Roukie686868/Presence-Sensor/Documents/Pictures/IMG_2770.jpg

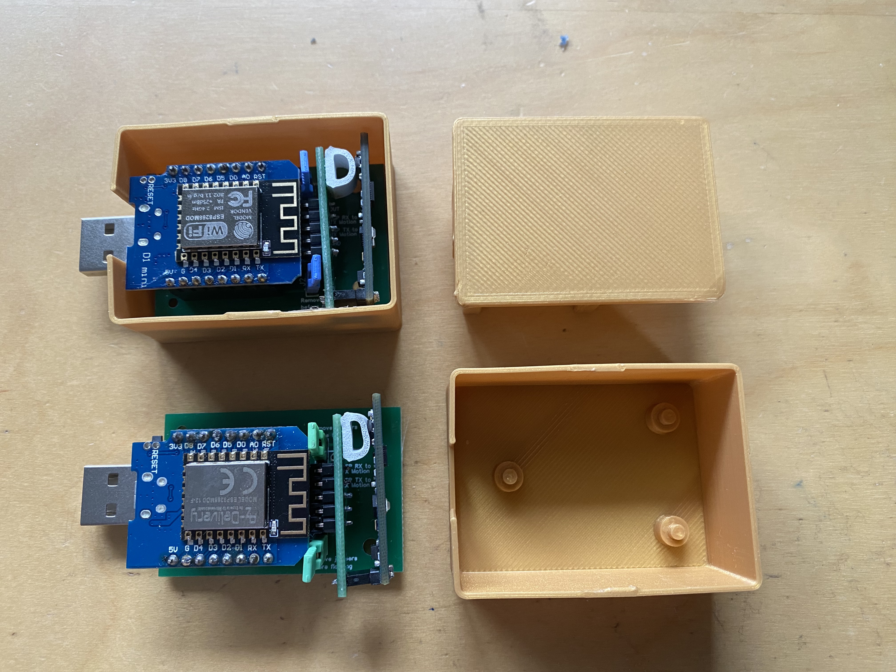
Documents/Pictures/IMG_2770.jpg
