Roukie686868/Presence-Sensor/Documents/Pictures/IMG_2771.jpg

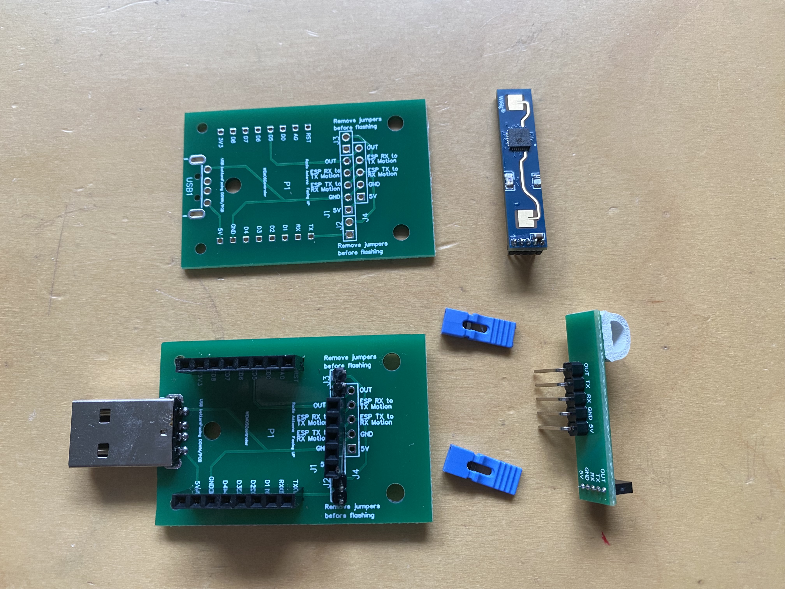
Documents/Pictures/IMG_2771.jpg
