Roukie686868/Presence-Sensor/Images/IMG_2784.jpg

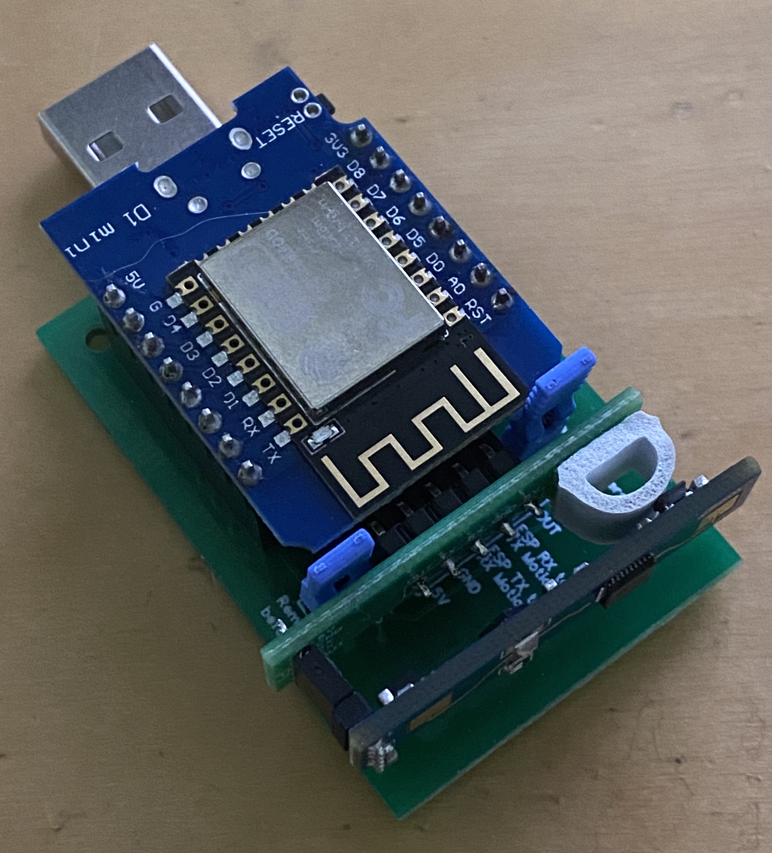
Images/IMG_2784.jpg
