Roukie686868/Presence-Sensor/Images/IMG_2785.jpg

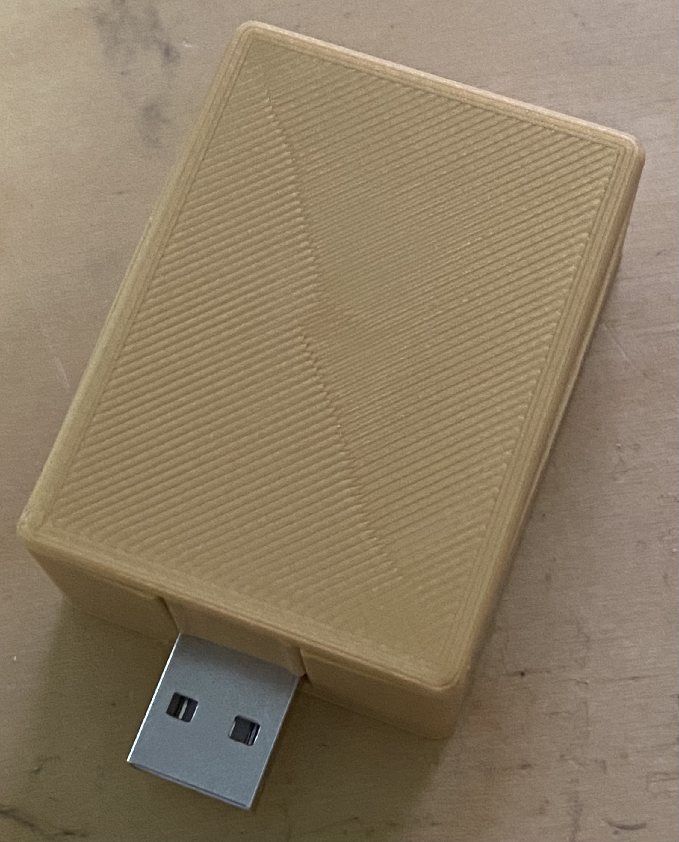
Images/IMG_2785.jpg
