Roukie686868/Presence-Sensor/Images/IMG_2786.jpg

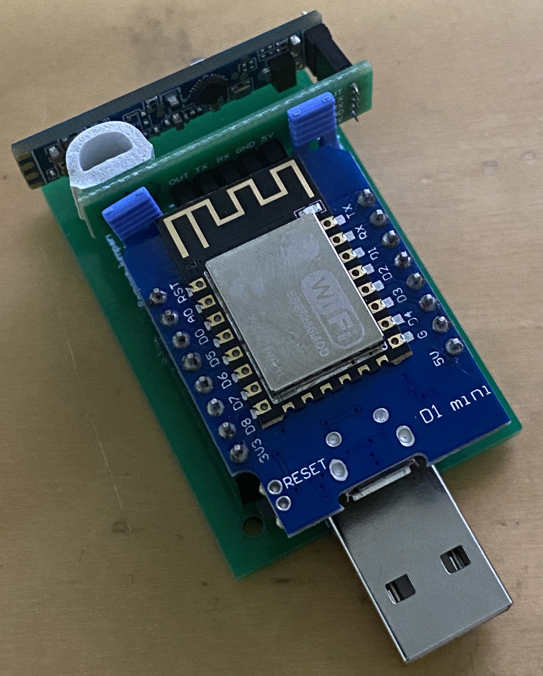
Images/IMG_2786.jpg
