Roukie686868/Presence-Sensor/Images/IMG_2787.jpg

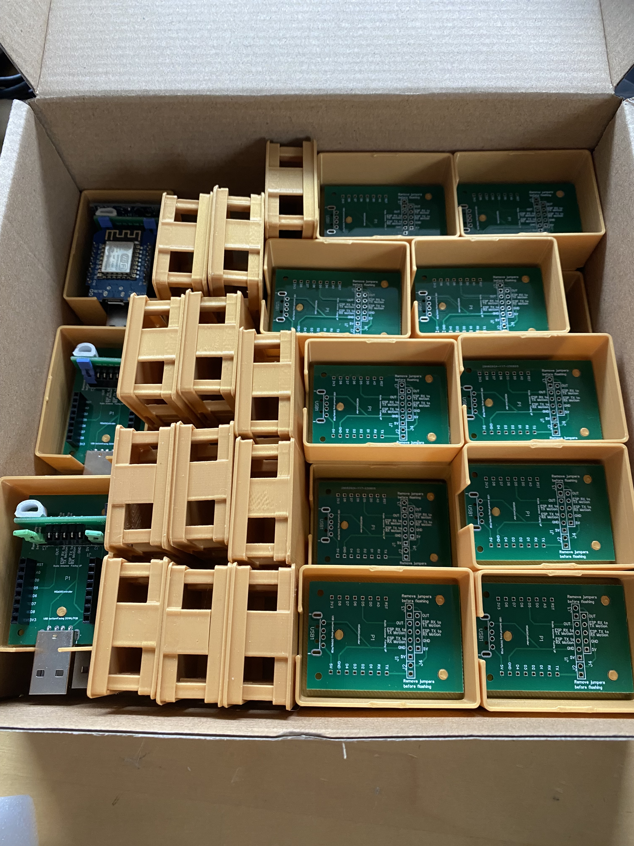
Images/IMG_2787.jpg
