Roukie686868/Presence-Sensor/Images/IMG_2789.jpg

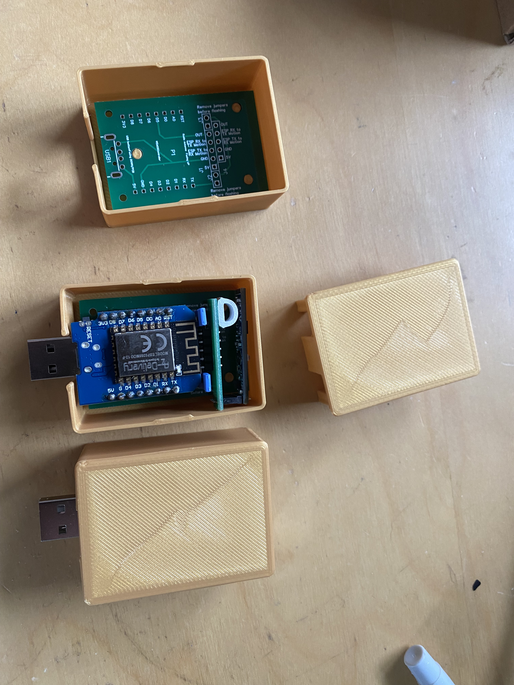
Images/IMG_2789.jpg
